RP6conrad/ESP-GPS-Logger/Ublox.cpp

#include "Ublox.h"
#include "Definitions.h"
//#include <EEPROM.h>
int Time_Set_OK;
bool Nav_rate_NACK = false;
bool High_nav_rate_ACK = false;
bool check_M10_nav_rate = false;

UBXMessage ubxMessage = {000000000000};//definition here, declaration in ublox.h !!
struct tm tmstruct ;
struct tm my_time;  // time elements structure
time_t unix_timestamp; // a timestamp

void Ublox_on(){
  pinMode(UBLOX_POWER1, OUTPUT);//Power beitian //default drive strength 2, only 2.7V @ ublox gps
  pinMode(UBLOX_POWER2, OUTPUT);//Power beitian
  pinMode(UBLOX_POWER3, OUTPUT);//Power beitiansee
  rtc_gpio_set_drive_capability(UBLOX_RTC_GPIO1,GPIO_DRIVE_CAP_3);// https://www.esp32.com/viewtopic.php?t=5840
  rtc_gpio_set_drive_capability(UBLOX_RTC_GPIO2,GPIO_DRIVE_CAP_3);//3.0V @ ublox gps current 50 mA
  gpio_set_drive_capability(UBLOX_GPIO3,GPIO_DRIVE_CAP_3);//rtc_gpio_ necessary, if not no output on RTC_pins 25 en 26, 13/3/2022
  delay(50);
  digitalWrite(UBLOX_POWER1, HIGH); 
  digitalWrite(UBLOX_POWER2, HIGH);
  digitalWrite(UBLOX_POWER3, HIGH);
  delay(100);
}
void Ublox_off(){
  digitalWrite(UBLOX_POWER1, LOW);
  digitalWrite(UBLOX_POWER2, LOW);
  digitalWrite(UBLOX_POWER3, LOW);
 // rtc_gpio_deinit(UBLOX_RTC_GPIO1);
 // rtc_gpio_deinit(UBLOX_RTC_GPIO2);
}
void Ublox_serial2(int delay_ms){
 for(int i=0;i<delay_ms;i++){
     int msgType = processGPS();
     if ( msgType == MT_NAV_ACK){
          Serial.print(" ACK ");
          Serial.print (ubxMessage.navAck.msg_cls);
          Serial.println (ubxMessage.navAck.msg_id);
          if(check_M10_nav_rate) High_nav_rate_ACK = true;
          }
     if ( msgType == MT_NAV_NACK){
          Serial.print(" NACK ");
          Serial.print (ubxMessage.navNack.msg_cls);
          Serial.println (ubxMessage.navNack.msg_id);
          if(check_M10_nav_rate) Nav_rate_NACK = true;
          }          
     if ( msgType == MT_NAV_ID){
          Serial.print("ID= :");
          Serial.print (ubxMessage.ubxId.ubx_id_1);
          Serial.print (ubxMessage.ubxId.ubx_id_2);
          Serial.print (ubxMessage.ubxId.ubx_id_3);
          Serial.print (ubxMessage.ubxId.ubx_id_4);
          Serial.println(ubxMessage.ubxId.ubx_id_5);
          }
     if ( msgType == MT_MON_GNSS){
          Serial.print("GNSS= :");
          Serial.print (ubxMessage.monGNSS.supported_Gnss);
          Serial.print (ubxMessage.monGNSS.default_Gnss);
          Serial.println (ubxMessage.monGNSS.enabled_Gnss);
          }
      if ( msgType == MT_MON_VER){
          Serial.print("SW Ublox=");
          Serial.println(ubxMessage.monVER.swVersion);
          Serial.print ("HW Ublox=");
          Serial.println (ubxMessage.monVER.hwVersion);
          }    
     delay(2);   
     } 
}
//Initialization of the ublox M8N with binary commands
void Init_ublox(void){
  int wait=250;
  char M8_9600_bd[20]="Ublox M8 9600bd";
  char M8_38400_bd[20]="Ublox M8 38400bd";
  if(config.ublox_type==M8_9600BD) strcpy(Ublox_type,M8_9600_bd);
  if(config.ublox_type==M8_38400BD) strcpy(Ublox_type,M8_38400_bd);
  /*send configuration data in UBX protocol is already done in SetupGPS()
  Serial.println("Set ublox UBX_OUT ");     
  for(int i = 0; i < sizeof(UBLOX_UBX_BD9600); i++) {                        
        Serial2.write( pgm_read_byte(UBLOX_UBX_BD9600+i) );
        }
  Ublox_serial2(wait); 
  */
  if(config.dynamic_model==1){
      Serial.println("Set ublox UBX_SEA ");
      for(int i = 0; i < sizeof(UBX_SEA); i++) {                        
        Serial2.write( pgm_read_byte(UBX_SEA+i) );
        }
  Ublox_serial2(wait);       
  }
  if(config.dynamic_model==2){
      Serial.println("Set ublox UBX_AUTOMOTIVE ");
      for(int i = 0; i < sizeof(UBX_AUTOMOTIVE); i++) {                        
        Serial2.write( pgm_read_byte(UBX_AUTOMOTIVE+i) );
        }
  Ublox_serial2(wait); 
  }
  //gnss 4 = GPS + GALILEO + BEIDOU  (default M10)
  //gnss x = GPS + GLONASS + BEIDOU   (impossible for the M10 ???)
  //gnss 3 = GPS + GLONASS + GALILEO
  //gnss 2 = GPS + GLONASS (default M8 ROM 2)
  //gnss 1 = GPS + GALILEO (not working for M8)
  //gnss 0 = GPS + BEIDOU  
    if(config.gnss==1){
      Serial.println("Set ublox UBX_GNSS2 : GPS + BEIDOU ");
      for(int i = 0; i < sizeof(UBX_GNSS2_GPS_BEIDOU); i++) {                        
        Serial2.write( pgm_read_byte(UBX_GNSS2_GPS_BEIDOU+i) );
        }
      Ublox_serial2(wait); 
      }
  if(config.gnss==3){
      Serial.println("Set ublox UBX_GNSS3 : GPS, GLONASS & GALILEO ");
      for(int i = 0; i < sizeof(UBX_GNSS3); i++) {                        
        Serial2.write( pgm_read_byte(UBX_GNSS3+i) );
        }
      Ublox_serial2(wait); 
      }
  if(config.gnss==4){
      Serial.println("Set ublox UBX_GNSS3 : GPS, GLONASS & BEIDOU ");
      for(int i = 0; i < sizeof(UBX_GNSS3_BEIDOU); i++) {                        
        Serial2.write( pgm_read_byte(UBX_GNSS3_BEIDOU+i) );
        }
      Ublox_serial2(wait); 
      }
  Serial.println("Check MON_GNSS settings ");
  for(int i = 0; i < sizeof(UBX_MON_GNSS); i++) {                        
      Serial2.write( pgm_read_byte(UBX_MON_GNSS+i) );
      }
  Ublox_serial2(wait); 
  Serial.print("Ask ublox Unique ID ");     
  for(int i = 0; i < sizeof(UBX_ID); i++) {                        
        Serial2.write( pgm_read_byte(UBX_ID+i) );
        }
  Ublox_serial2(wait);
  Serial.println("Check UBX_MON_VER ");     
   for(int i = 0; i < sizeof(UBX_MON_VER); i++) {                        
        Serial2.write( pgm_read_byte(UBX_MON_VER+i) );        
        }                 
  Ublox_serial2(wait);
  Serial.println("Set ublox NAV_PVT_ON ");   
  for(int i = 0; i < sizeof(UBLOX_UBX_NAVPVT_ON); i++) {                        
        Serial2.write( pgm_read_byte(UBLOX_UBX_NAVPVT_ON+i) );
        }
  Ublox_serial2(wait);         
  Serial.println("Set ublox NAV_DOP_ON ");   
  for(int i = 0; i < sizeof(UBLOX_UBX_NAVDOP_ON); i++) {                        
        Serial2.write( pgm_read_byte(UBLOX_UBX_NAVDOP_ON+i) );
        }
  Ublox_serial2(wait); 
  if((config.logUBX_nav_sat)&(config.logUBX)){
      Serial.println("Set ublox NAV_SAT_ON ");   
      for(int i = 0; i < sizeof(UBLOX_UBX_NAVSAT_ON); i++) {                        
            Serial2.write( pgm_read_byte(UBLOX_UBX_NAVSAT_ON+i) );
            }
      Ublox_serial2(wait);   
      }
  Serial.println("Set ublox to 38400BD "); 
  for(int i = 0; i < sizeof(UBLOX_UBX_BD38400); i++) {                        
        Serial2.write( pgm_read_byte(UBLOX_UBX_BD38400+i) );
        //delay(5); // simulating a 38400baud pace (or less), otherwise commands are not accepted by the device.
        } 
  Serial2.flush();
  Serial2.begin(38400,SERIAL_8N1, RXD2, TXD2);//in Init_ublox last command is change baudrate to 19200, necessary for 10 Hz  NAV_PVT + NAV_DOP!!!
  Ublox_serial2(wait);    
}
//Initialization of the ublox M8N  rate with binary commands, choice between 1..4
void Set_rate_ublox(int rate){
  int sample_rate=2;
  switch(rate){
    case 1:sample_rate=2;break;
    case 2:sample_rate=3;break;
    case 4:sample_rate=4;break;
    case 5:sample_rate=5;break;
    case 8:sample_rate=6;break;
    case 10:sample_rate=7;break;
    case 18:sample_rate=8;break;
    default:sample_rate=2;
    config.sample_rate=1;
    }
  Serial.print("Set rate Ublox ");
  for(int i = (sample_rate*14-14); i < sample_rate*14; i++) {                        
        Serial2.write( pgm_read_byte(UBLOX_RATE+i) );
        }
  Ublox_serial2(500);      
}
void sendNavSpgInfilMaxSvs(uint8_t maxSvs) {
  if(maxSvs<10)maxSvs=10;
  uint8_t packet[17] = {
    0xB5, 0x62,             // Sync
    0x06, 0x8A,             // Class, ID
    0x09, 0x00,             // Payload Length (9)
    0x00,                   // Version
    0x01,                   // Layer: 0x01 = RAM
    0x00, 0x00,             // Reserved
    0xA2, 0x00, 0x11, 0x20, // Key ID (Little Endian)
    maxSvs,                 // De dynamische waarde
    0x00, 0x00              // Placeholder for CK_A, CK_B
  };
  uint8_t ck_a = 0;
  uint8_t ck_b = 0;
  // Calculate checksum start at index 2 (Class/ID to Value)
  for (int i = 2; i < 15; i++) {
    ck_a += packet[i];
    ck_b += ck_a;
  }
  // add checksum last 2 bytes
  packet[15] = ck_a;
  packet[16] = ck_b;
  // send to gps module
  Serial2.write(packet, sizeof(packet));
  Ublox_serial2(500);   //wait for response
}

//Initialization of the ublox M10N with binary commands
void Init_ubloxM10(void){
  int wait=250;
  char M9_9600_bd[20]="Ublox M9 9600bd";
  char M9_38400_bd[20]="Ublox M9 38400bd";
  char M9_115200_bd[20]="Ublox M9 115200bd";
  char M10_9600_bd[20]="Ublox M10 9600bd";
  char M10_38400_bd[20]="Ublox M10 38400bd";
  char M10_115200_bd[20]="Ublox M10 115200bd";
  if(config.ublox_type==M9_9600BD) strcpy(Ublox_type,M9_9600_bd);
  if(config.ublox_type==M9_38400BD) strcpy(Ublox_type,M9_38400_bd);
  if(config.ublox_type==M9_115200BD) strcpy(Ublox_type,M9_115200_bd);
  if(config.ublox_type==M10_9600BD) strcpy(Ublox_type,M10_9600_bd);
  if(config.ublox_type==M10_38400BD) strcpy(Ublox_type,M10_38400_bd);
  if(config.ublox_type==M10_115200BD) strcpy(Ublox_type,M10_115200_bd);
  //send configuration data in UBX protocol 
  Serial.println("Set ublox M10 NMEA OFF ");     
  for(int i = 0; i < sizeof(UBLOX_M10_NMEA_OFF); i++) {                        
        Serial2.write( pgm_read_byte(UBLOX_M10_NMEA_OFF+i) );
        }
  Ublox_serial2(wait); 
  if((config.ublox_type == M10_9600BD)|(config.ublox_type == M10_38400BD)|(config.ublox_type == M10_115200BD)){
    if(config.M10_high_nav == SET_M10_HIGH_NAV){ Set_M10_high_nav_rate();}//reboot noodzakelijk ????
    //config.M10_high_nav=Check_M10_nav_rate();
    }
   
  if(config.dynamic_model==1){
      Serial.println("Set ublox UBX_M10_SEA ");
      for(int i = 0; i < sizeof(UBX_M10_SEA); i++) {                        
        Serial2.write( pgm_read_byte(UBX_M10_SEA+i) );
        }
  Ublox_serial2(wait);       
  }
  if(config.dynamic_model==2){
      Serial.println("Set ublox UBX_M10_AUTOMOTIVE ");
      for(int i = 0; i < sizeof(UBX_M10_AUTOMOTIVE); i++) {                        
        Serial2.write( pgm_read_byte(UBX_M10_AUTOMOTIVE+i) );
        }
  Ublox_serial2(wait); 
  }
  //Default M10 = GPS+GALILEO+BEIDOU
  //GNSS 5 = GPS + GALILEO + GLONASS + BEIDOU (only M9)
  //gnss 4 = GPS + GALILEO + BEIDOU_B1C  (default is beidou B1L !! M10)
  //gnss x = GPS + GLONASS + BEIDOU (switch off QZSS first M10 !!!)
  //gnss 3 = GPS + GLONASS + GALILEO
  //gnss 2 = GPS + GLONASS
  //gnss 1 = GPS + GALILEO
  
  if(config.gnss==4){   //for M9, default is 4 GNSS activated, config.gnss=6  !!
        Serial.println("Set ublox M10 GLONASS OFF ");     
        for(int i = 0; i < sizeof(UBLOX_M10_GLONASS_OFF); i++) {                        
              Serial2.write( pgm_read_byte(UBLOX_M10_GLONASS_OFF+i) );
              }
        Ublox_serial2(wait);
        Serial.println("Set ublox M10 BEIDOU B1 OFF ");     
        for(int i = 0; i < sizeof(UBLOX_M10_BEIDOU_B1_OFF); i++) {                        
              Serial2.write( pgm_read_byte(UBLOX_M10_BEIDOU_B1_OFF+i) );
              }
        Ublox_serial2(wait);
        Serial.println("Set ublox M10 BEIDOU B1C ON ");     
        for(int i = 0; i < sizeof(UBLOX_M10_BEIDOU_B1C_ON); i++) {                        
              Serial2.write( pgm_read_byte(UBLOX_M10_BEIDOU_B1C_ON+i) );
              }
        Ublox_serial2(wait);
        }     
  if(((config.gnss==5)&(config.sample_rate<10)&((config.ublox_type == M10_9600BD)|(config.ublox_type == M10_38400BD)|(config.ublox_type == M10_115200BD)))){  
        Serial.println("Set ublox M10 4 GNSS ");     
        for(int i = 0; i < sizeof(UBLOX_M10_4GNSS); i++) {                        
              Serial2.write( pgm_read_byte(UBLOX_M10_4GNSS+i) );
              }
        Ublox_serial2(wait);
        }            
  if(config.gnss==3){          
      Serial.println("Set ublox M10 BEIDOU OFF ");     
      for(int i = 0; i < sizeof(UBLOX_M10_BEIDOU_OFF); i++) {                        
            Serial2.write( pgm_read_byte(UBLOX_M10_BEIDOU_OFF+i) );
            }
      Ublox_serial2(wait);  
      Serial.println("Set ublox M10 GLONASS ON ");     
      for(int i = 0; i < sizeof(UBLOX_M10_GLONASS_ON); i++) {                        
            Serial2.write( pgm_read_byte(UBLOX_M10_GLONASS_ON+i) );
            }
      Ublox_serial2(wait);      
      } 
  if(config.gnss==2){          
      Serial.println("Set ublox M10 GALILEO OFF ");     
      for(int i = 0; i < sizeof(UBLOX_M10_GAL_OFF); i++) {                        
            Serial2.write( pgm_read_byte(UBLOX_M10_GAL_OFF+i) );
            }
      Ublox_serial2(wait);
      Serial.println("Set ublox M10 BEIDOU OFF ");     
      for(int i = 0; i < sizeof(UBLOX_M10_BEIDOU_OFF); i++) {                        
            Serial2.write( pgm_read_byte(UBLOX_M10_BEIDOU_OFF+i) );
            }
      Ublox_serial2(wait);  
      Serial.println("Set ublox M10 GLONASS ON ");     
      for(int i = 0; i < sizeof(UBLOX_M10_GLONASS_ON); i++) {                        
            Serial2.write( pgm_read_byte(UBLOX_M10_GLONASS_ON+i) );
            }
      Ublox_serial2(wait);      
      }
  if(config.gnss==1){     
      Serial.println("Set ublox M10 BEIDOU OFF ");     
      for(int i = 0; i < sizeof(UBLOX_M10_BEIDOU_OFF); i++) {                        
            Serial2.write( pgm_read_byte(UBLOX_M10_BEIDOU_OFF+i) );
            }
      Ublox_serial2(wait);      
      Serial.println("Set ublox M10 GLONASS OFF ");     
      for(int i = 0; i < sizeof(UBLOX_M10_GLONASS_OFF); i++) {                        
            Serial2.write( pgm_read_byte(UBLOX_M10_GLONASS_OFF+i) );
            }
      Ublox_serial2(wait);      
      }         
  Serial.println("Set ublox M10 UBX On ");     
  for(int i = 0; i < sizeof(UBLOX_M10_UBX); i++) {                        
        Serial2.write( pgm_read_byte(UBLOX_M10_UBX+i) );
        }
  Ublox_serial2(wait);    
  Serial.println("Set ublox M10 NAV_PVT_ON ");   
  for(int i = 0; i < sizeof(UBLOX_M10_NAV_PVT); i++) {                        
        Serial2.write( pgm_read_byte(UBLOX_M10_NAV_PVT+i) );
        }
  Ublox_serial2(wait);         
  Serial.println("Set ublox M10 NAV_DOP_ON ");   
  for(int i = 0; i < sizeof(UBLOX_M10_NAV_DOP); i++) {                        
        Serial2.write( pgm_read_byte(UBLOX_M10_NAV_DOP+i) );
        }
  /**     
  if(config.M10_full_power){
    Serial.println("Set ublox M10 full power ON ");   
    for(int i = 0; i < sizeof(UBX_M10_FULL_POWER_MODE); i++) {                        
          Serial2.write( pgm_read_byte(UBX_M10_FULL_POWER_MODE+i) );
          }      
    Ublox_serial2(wait);
    } 
  */  
  Serial.println("Set ublox max_Svs ");   
  sendNavSpgInfilMaxSvs(config.max_Svs); //max satellites in nav solution  
  Serial.println("Set ublox min elevation Sats ");  
  build_ubx_cfg_min_elevation(config.M10_min_elevation); //minimal elevation above horizon

  if((config.logUBX_nav_sat)&(config.logUBX)){
      Serial.println("Set ublox M10 NAV_SAT_ON "); 
      if(config.sample_rate<10){ 
        for(int i = 0; i < sizeof(UBLOX_M10_NAV_SAT); i++) {     //NAV_SAT_RATE = sample_rate/10                   
        Serial2.write( pgm_read_byte(UBLOX_M10_NAV_SAT+i) );
        }
      } 
      else{
        for(int i = 0; i < sizeof(UBLOX_M9_NAV_SAT); i++) {       //NAV_SAT_RATE = sample_rate/40                  
        Serial2.write( pgm_read_byte(UBLOX_M9_NAV_SAT+i) );
        }  
      }
      Ublox_serial2(wait);
    }       
  Serial.println("Check UBX_MON_VER ");  //does this work for the M10 ??   
   for(int i = 0; i < sizeof(UBX_MON_VER); i++) {                        
        Serial2.write( pgm_read_byte(UBX_MON_VER+i) );        
        }           
  Ublox_serial2(wait); 
  Serial.println("Check MON_GNSS settings ");
  for(int i = 0; i < sizeof(UBX_MON_GNSS); i++) {                        
      Serial2.write( pgm_read_byte(UBX_MON_GNSS+i) );
      }
  Ublox_serial2(wait);      
  Serial.print("Ask ublox Unique ID ");     
  for(int i = 0; i < sizeof(UBX_ID); i++) {                        
        Serial2.write( pgm_read_byte(UBX_ID+i) );
        }  
  Ublox_serial2(wait); 
  Serial.println("Set ublox M10 to 38400BD "); 
  for(int i = 0; i < sizeof(UBLOX_M10_UBX_BD38400); i++) {                        
        Serial2.write( pgm_read_byte(UBLOX_M10_UBX_BD38400+i) );
        //delay(5); // simulating a 38400baud pace (or less), otherwise commands are not accepted by the device.
        } 
  Serial2.flush();
  Serial2.begin(38400,SERIAL_8N1, RXD2, TXD2);//in Init_ublox last command is change baudrate to 38400, necessary for 10 Hz  NAV_PVT + NAV_DOP!!!
  Ublox_serial2(wait);   
}
//Initialization of the ublox M10N  rate with binary commands, choice between 1..5
void Set_rate_ubloxM10(int rate){
  int sample_rate=2;
  switch(rate){
    case 1:sample_rate=1;break;
    case 2:sample_rate=2;break;
    case 4:sample_rate=3;break;
    case 5:sample_rate=4;break;
    case 8:sample_rate=5;break;
    case 10:sample_rate=6;break;
    case 15:sample_rate=7;break;
    case 20:sample_rate=8;break;
    default:sample_rate=1;
    config.sample_rate=1;
    }
  Serial.print("Set rate Ublox M10");
  for(int i = (sample_rate*18-18); i < sample_rate*18; i++) {                        
        Serial2.write( pgm_read_byte(UBLOX_M10_RATE+i) );
        }
  Ublox_serial2(500);      
}
int Set_GPS_Time(float time_offset){    
  // convert a date and time into unix time
        if(ubxMessage.navPvt.year<2023) {
          //Serial.println("GPS Reported year not plausible (<2023) !");
          return false; 
          }//check if year is plausible 
        my_time.tm_sec = ubxMessage.navPvt.second;
        my_time.tm_hour = ubxMessage.navPvt.hour;
        my_time.tm_min = ubxMessage.navPvt.minute;
        my_time.tm_mday = ubxMessage.navPvt.day;
        my_time.tm_mon = ubxMessage.navPvt.month-1;  //mktime needs months 0 - 11  
        my_time.tm_year = ubxMessage.navPvt.year - 1900; // mktime needs years since 1900, so deduct 1900
        //my_time.tm_isdst = 1;//daylight timesaving active
        //# define DLS
        #if defined(DLS)
        //summertime is on march 26 2023 2 AM, see https://www.di-mgt.com.au/wclock/help/wclo_tzexplain.html     
        my_time.tm_hour = 2;
        my_time.tm_min = 58;
        my_time.tm_mday =26;
        my_time.tm_mon = 2;  //mktime needs months 0 - 11  
        my_time.tm_year = 2023 - 1900; 
        #endif
        setenv("TZ","GMT0",1);//neede if time is set again (gps sets time double)
        tzset();
        unix_timestamp =  mktime(&my_time);//mktime returns local time, so TZ is important !!!
        struct timeval tv = { .tv_sec = (time_t)(unix_timestamp), .tv_usec = 0 };  //clean utc time !!     
        settimeofday(&tv, NULL);
        setenv("TZ",TimeZone,1);
        tzset();     //this works for CET, but TZ string is different for every Land / continent....
        delay(10);//
        if(!getLocalTime(&tmstruct)){
            Serial.println("Can't get time1...");
            return false;
            }
        if((tmstruct.tm_year+1900)<2023){
          Serial.printf("\nNow is : %d-%02d-%02d %02d:%02d:%02d\n",(tmstruct.tm_year)+1900,( tmstruct.tm_mon)+1, tmstruct.tm_mday,tmstruct.tm_hour , tmstruct.tm_min, tmstruct.tm_sec);
          //Serial.println("GPS Reported year not plausible (<2023) !");
          return false; 
          }
        Serial.println("GPS Local Time is set");
        return true;
}

// The last two bytes of the message is a checksum value, used to confirm that the received payload is valid.
// The procedure used to calculate this is given as pseudo-code in the uBlox manual.
void calcChecksum(unsigned char* CK,int msgType, int msgSize) {
  memset(CK, 0, 2);
  for (int i = 0; i < msgSize; i++) {
    if(msgType==MT_NAV_PVT) {CK[0] += ((unsigned char*)(&ubxMessage.navPvt))[i];}
    else if(msgType==MT_NAV_DOP) {CK[0] += ((unsigned char*)(&ubxMessage.navDOP))[i];} 
    else if(msgType==MT_MON_GNSS){CK[0] += ((unsigned char*)(&ubxMessage.monGNSS))[i];} 
    else if(msgType==MT_MON_VER){CK[0] += ((unsigned char*)(&ubxMessage.monVER))[i];} 
    else if(msgType==MT_NAV_ACK){CK[0] += ((unsigned char*)(&ubxMessage.navAck))[i];} 
    else if(msgType==MT_NAV_NACK){CK[0] += ((unsigned char*)(&ubxMessage.navNack))[i];} 
    else if(msgType==MT_NAV_SAT){CK[0] += ((unsigned char*)(&ubxMessage.navSat))[i];} 
    else if(msgType==MT_NAV_ID){CK[0] += ((unsigned char*)(&ubxMessage.ubxId))[i];} 
    else {CK[0] += ((unsigned char*)(&ubxMessage))[i];}
    CK[1] += CK[0];
  }
}
// Compares the first two bytes of the ubxMessage struct with a specific message header.
// Returns true if the two bytes match (0xB5 0x62).
boolean compareMsgHeader(const unsigned char* msgHeader) {
  unsigned char* ptr = (unsigned char*)(&ubxMessage.navDummy);
  return ptr[0] == msgHeader[0] && ptr[1] == msgHeader[1];
}
// Reads in bytes from the GPS module and checks to see if a valid message has been constructed.
// Returns the type of the message found if successful, or MT_NONE if no message was found.
// After a successful return the contents of the ubxMessage union will be valid, for the 
// message type that was found. As now every message has its own struct, further calls to this function can invalidate the
// message content if the message was the same, so you must use the obtained values before calling this function again.

int processGPS() {
  static int fpos = 0;
  static unsigned char checksum[2];
  static byte currentMsgType = MT_NONE;
  static int payloadSize = sizeof(ubxMessage.navDummy);
  //static uint16_t len;//10 Hz M10 issue ??
  while ( Serial2.available() ) {
    byte c = Serial2.read();    
    //Serial.write(c);
    if ( fpos < 2 ) {
      // For the first two bytes we are simply looking for a match with the UBX header bytes (0xB5,0x62)
      if ( c == UBX_HEADER[fpos] )
        fpos++;
      else
        fpos = 0; // Reset to beginning state.
    }
    else {
      // If we come here then fpos >= 2, which means we have found a match with the UBX_HEADER
      // and we are now reading in the bytes that make up the payload.
      // Place the incoming byte into the ubxMessage.navDummy struct. The position is fpos-2 because
      // the struct does not include the initial two-byte header (UBX_HEADER).
      // the struct does not include the 2 last bytes which are the checksums
      // checksums are not placed in the ubxMessage !!!
      if (((fpos-2) < payloadSize)&(fpos<4)){((unsigned char*)(&ubxMessage.navDummy))[fpos-2] = c;} 
      if(fpos==3) {
        // We have just received the second byte of the message type header, 
        // so now we can check to see what kind of message it is.
        //We have to restore cls and id to the correct substructure
        if ( compareMsgHeader(NAV_PVT_HEADER) ) {
          currentMsgType = MT_NAV_PVT;
          payloadSize = sizeof(NAV_PVT);
          ubxMessage.navPvt.cls=ubxMessage.navDummy.cls;
          ubxMessage.navPvt.id=ubxMessage.navDummy.id;
          //Serial.print("hPVT ");
        }
        else if ( compareMsgHeader(MON_GNSS_HEADER) ) {
          currentMsgType = MT_MON_GNSS;
          payloadSize = sizeof(MON_GNSS);
          ubxMessage.monGNSS.cls=ubxMessage.navDummy.cls;
          ubxMessage.monGNSS.id=ubxMessage.navDummy.id;
          //Serial.println("MT_MON_GNSS\n");
        }
        else if ( compareMsgHeader(NAV_DOP_HEADER) ) {
          currentMsgType = MT_NAV_DOP;
          payloadSize = sizeof(NAV_DOP);
          ubxMessage.navDOP.cls=ubxMessage.navDummy.cls;
          ubxMessage.navDOP.id=ubxMessage.navDummy.id;
          //Serial.print("hDOP ");
        }
        else if ( compareMsgHeader(MON_VER_HEADER) ) {
          currentMsgType = MT_MON_VER;
          payloadSize = sizeof(MON_VER);
          ubxMessage.monVER.cls=ubxMessage.navDummy.cls;
          ubxMessage.monVER.id=ubxMessage.navDummy.id;
          //Serial.println("MT_MON_VER\n");
        }
        else if ( compareMsgHeader(NAV_ACK_HEADER) ) {
          currentMsgType = MT_NAV_ACK;
          payloadSize = sizeof(NAV_ACK);
          ubxMessage.navAck.cls=ubxMessage.navDummy.cls;
          ubxMessage.navAck.id=ubxMessage.navDummy.id;
          //Serial.println("NAV_ACK\n");
        }
        else if ( compareMsgHeader(NAV_NACK_HEADER) ) {
          currentMsgType = MT_NAV_NACK;
          payloadSize = sizeof(NAV_NACK);
          ubxMessage.navNack.cls=ubxMessage.navDummy.cls;
          ubxMessage.navNack.id=ubxMessage.navDummy.id;
          //Serial.println("NAV_NACK\n");
        }
        else if ( compareMsgHeader(NAV_SAT_HEADER) ) {
          currentMsgType = MT_NAV_SAT;
          ubxMessage.navSat.cls=ubxMessage.navDummy.cls;
          ubxMessage.navSat.id=ubxMessage.navDummy.id;
          //Serial.println("NAV_SAT\n");
        }
        else if ( compareMsgHeader(NAV_ID_HEADER) ) {
          currentMsgType = MT_NAV_ID;
          ubxMessage.ubxId.cls=ubxMessage.navDummy.cls;
          ubxMessage.ubxId.id=ubxMessage.navDummy.id;
          //Serial.println("NAV_ID\n");
        }
        else {
          // unknown message type, bail
          currentMsgType = MT_NONE;
          fpos = 0;
          continue;
        }
      }
      if (((fpos-2) < payloadSize)&(fpos>=4)){
        if(currentMsgType==MT_NAV_PVT) {((unsigned char*)(&ubxMessage.navPvt))[fpos-2] = c;} 
        if(currentMsgType==MT_NAV_DOP) {((unsigned char*)(&ubxMessage.navDOP))[fpos-2] = c;} 
        if(currentMsgType==MT_MON_GNSS) {((unsigned char*)(&ubxMessage.monGNSS))[fpos-2] = c;} 
        if(currentMsgType==MT_MON_VER) {((unsigned char*)(&ubxMessage.monVER))[fpos-2] = c;} 
        if(currentMsgType==MT_NAV_ACK) {((unsigned char*)(&ubxMessage.navAck))[fpos-2] = c;} 
        if(currentMsgType==MT_NAV_NACK) {((unsigned char*)(&ubxMessage.navNack))[fpos-2] = c;} 
        if(currentMsgType==MT_NAV_SAT) {((unsigned char*)(&ubxMessage.navSat))[fpos-2] = c;}
        if(currentMsgType==MT_NAV_ID) {((unsigned char*)(&ubxMessage.ubxId))[fpos-2] = c;}  
      }
       if (fpos==6){
        if(currentMsgType==MT_NAV_PVT){ubxMessage.navPvt.len=payloadSize-6;}//safety if .len is wrong
        if(currentMsgType==MT_NAV_DOP){ubxMessage.navDOP.len=payloadSize-6;}//safety if .len is wrong
        if(currentMsgType==MT_NAV_ID){ payloadSize=ubxMessage.ubxId.len+6;}// .len = 9 bytes for M8, but 10 bytes for M10
        if(currentMsgType==MT_MON_VER){
            if(ubxMessage.monVER.len+6<sizeof(ubxMessage.monVER)){
                payloadSize=ubxMessage.monVER.len+6;
                }//M10 has extensions ??
            else{fpos=0;}//something went wrong, start over again !!!
            }          
        if(currentMsgType==MT_NAV_SAT){
            if(ubxMessage.navSat.len+6<sizeof(ubxMessage.navSat)){//safety if .len is wrong
                payloadSize=ubxMessage.navSat.len+6;
                }//payload is variable with nav_sat msg
            else{fpos=0;}//something went wrong, start over again !!!
            }
      }
      fpos++;
      if ( fpos == (payloadSize) ) {//was (payloadSize+2)
      // All payload bytes have now been received, so we can calculate the 
      // expected checksum value to compare with the next two incoming bytes.
      // checksum has to calculated out of the correct substructure !!!
        calcChecksum(checksum,currentMsgType,payloadSize-2);//was payload !!
      }
      else if ( fpos == (payloadSize+1) ) {//was (payloadSize+3)   fpos-3=c, of payloadsize+1-3=c, dus payloadsize-2
        // First byte after the payload, ie. first byte of the checksum.
        // Does it match the first byte of the checksum we calculated?

        if ( c != checksum[0] ) {
          // Checksum doesn't match, reset to beginning state and try again.
           Serial.println("CkA NIO");
         if ((Time_Set_OK==true)&(nav_pvt_message>10)){
              char tekst[32] = "";
              sprintf(tekst, "ChecksumA_NIO @ %d\n", (nav_pvt_message-11));
              logERR(tekst);
            }
          fpos = 0; 
        }
      }
      else if ( fpos == (payloadSize+2) ) {//was (payloadSize+4)  fpos-4=c, of payloadsize+1-4=c, dus payloadsize-1
        // Second byte after the payload, ie. second byte of the checksum.
        // Does it match the second byte of the checksum we calculated?
        fpos = 0; // We will reset the state regardless of whether the checksum matches.
        if ( c == checksum[1] ) {
          // Checksum matches, we have a valid message.
          /* iTow has a 18 s diff with UTC, issue with GPS Results !!
           if(currentMsgType==MT_NAV_SAT){
              ubxMessage.navSat.iTOW=ubxMessage.navSat.iTOW-18*1000;//to match 18s diff UTC nav pvt & GPS nav sat !!!
              calcChecksum(checksum,currentMsgType,payloadSize-2);//have to calculate new checksum !!
              ((unsigned char*)(&ubxMessage.navSat))[payloadSize-2]=checksum[0];//checksum is not on a fixed pos, depends from the payload !!!
              ((unsigned char*)(&ubxMessage.navSat))[payloadSize-1]=checksum[1];//checksum is not on a fixed pos, depends from the payload !!!
            }
          */ 
          return currentMsgType; 
        }
        else{ if ((Time_Set_OK==true)&(nav_pvt_message>10)){
              Serial.println("CkB NIO");
              char tekst[32] = "";
              sprintf(tekst, "ChecksumB_NIO @ %d\n", (nav_pvt_message-11));
              logERR(tekst);
              }
            }
      }    
      else if ( fpos > (payloadSize+2) ) {//was (payloadSize+4)
        // We have now read more bytes than both the expected payload and checksum 
        // together, so something went wrong. Reset to beginning state and try again.
        fpos = 0;
      }
    }
  }
  return MT_NONE;
}
int Auto_detect_ublox(){
  config.ublox_type=0;
  bool Ublox_M10=false;
  Serial.println("Check UBX_MON_VER @9600bd ");  //check for 9600 bd ??   
  for(int i = 0; i < sizeof(UBX_MON_VER); i++) {                        
        Serial2.write( pgm_read_byte(UBX_MON_VER+i) );        
        }           
  Ublox_serial2(1000); 
  Serial.println(ubxMessage.monVER.hwVersion[3]);
  if(ubxMessage.monVER.hwVersion[3]=='8'){
    config.ublox_type=M8_9600BD;
    Serial.println("Ublox M8 @9600bd ");
    }//M8@9600 bd
  if(ubxMessage.monVER.hwVersion[3]=='9'){
    config.ublox_type=M9_9600BD;
    Serial.println("Ublox M9 @9600bd ");
    }//M9@9600 bd  
  if(ubxMessage.monVER.hwVersion[3]=='A'){
    config.ublox_type=M10_9600BD;
    Serial.println("Ublox M10 @9600bd ");
    Ublox_M10=true;
    }//M10@9600 bd
  if(config.ublox_type==0){//no ublox @9600 bd detected
      //Serial2.flush();
      Serial2.begin(38400,SERIAL_8N1, RXD2, TXD2);// Change baudrate to 38400 for new test
      Serial2.flush();
      Serial.println("Check UBX_MON_VER @38400bd ");  //check for 9600 bd ?? 
      delay(100);  
      for(int i = 0; i < sizeof(UBX_MON_VER); i++) {                        
            Serial2.write( pgm_read_byte(UBX_MON_VER+i) );        
            }           
      Ublox_serial2(1000); 
      if(ubxMessage.monVER.hwVersion[3]=='8'){
        config.ublox_type=M8_38400BD;
        Serial.println("Ublox M8 @38400bd ");
        }//M8@384000 bd
      if(ubxMessage.monVER.hwVersion[3]=='9'){
        config.ublox_type=M9_38400BD;
        Serial.println("Ublox M9 @38400bd ");
        }//M8@384000 bd  
      if(ubxMessage.monVER.hwVersion[3]=='A'){
        config.ublox_type=M10_38400BD;
        Serial.println("Ublox M10 @38400bd ");
        Ublox_M10=true;
        }
      }
  if(config.ublox_type==0){//no ublox @9600 bd detected
      Serial2.begin(115200,SERIAL_8N1, RXD2, TXD2);// Change baudrate to 38400 for new test
      Serial2.flush();
      Serial.println("Check UBX_MON_VER @115200bd ");  //check for 9600 bd ?? 
      delay(100);  
      for(int i = 0; i < sizeof(UBX_MON_VER); i++) {                        
            Serial2.write( pgm_read_byte(UBX_MON_VER+i) );        
            }           
      Ublox_serial2(1000); 
      if(ubxMessage.monVER.hwVersion[3]=='8'){
        config.ublox_type=M8_115200BD;
        Serial.println("Ublox M8 @115200bd ");
        }
      if(ubxMessage.monVER.hwVersion[3]=='9'){
        config.ublox_type=M9_115200BD;
        Serial.println("Ublox M9 @115200bd ");
        } 
      if(ubxMessage.monVER.hwVersion[3]=='A'){
        config.ublox_type=M10_115200BD;
        Serial.println("Ublox M10 @115200bd ");
        Ublox_M10=true;
        }
      }  
    Serial.println(ubxMessage.monVER.hwVersion[3]) ; 
    if(Ublox_M10==true){
      config.M10_high_nav=Check_M10_nav_rate();
      //EEPROM.write(1,config.M10_high_nav);EEPROM.commit();
      preferences.begin("gps_config", false);
      config.M10_high_nav=Check_M10_nav_rate();
      preferences.putUChar("M10_high_nav",config.M10_high_nav);
      preferences.end();
      }
    return config.ublox_type;  
}
/*
int Check_M10_nav_rate(void){
  int result=NO_M10_GPS;
  check_M10_nav_rate=true;
  Serial.println("Get M10 NAV Rate ");
    for(int i = 0; i < sizeof(UBX_M10_GET_NAV_RATE); i++) {                        
    Serial2.write( pgm_read_byte(UBX_M10_GET_NAV_RATE+i) );
    }
  Nav_rate_NACK = false;
  High_nav_rate_ACK = false;      
  Ublox_serial2(500);
  check_M10_nav_rate = false;
  if(Nav_rate_NACK){ 
    Serial.println("M10 Default Nav Rate");
    result=M10_DEFAULT_NAV;
    if(EEPROM.readByte(1)!=M10_DEFAULT_NAV)EEPROM.writeByte(1,M10_DEFAULT_NAV); EEPROM.commit();
  }
  if(High_nav_rate_ACK){
    Serial.println("M10 High Nav Rate set");
    result=M10_HIGH_NAV_RATE;
    if(EEPROM.readByte(1)!=M10_HIGH_NAV_RATE)EEPROM.writeByte(1,M10_HIGH_NAV_RATE); EEPROM.commit();
    } 
    return result;       
  }
*/  
int Check_M10_nav_rate(void){
  int result = NO_M10_GPS;
  check_M10_nav_rate = true;
  Serial.println(F("Get M10 NAV Rate "));
  
  for(int i = 0; i < sizeof(UBX_M10_GET_NAV_RATE); i++) {                        
    Serial2.write( pgm_read_byte(UBX_M10_GET_NAV_RATE+i) );
  }
  
  Nav_rate_NACK = false;
  High_nav_rate_ACK = false;      
  Ublox_serial2(500);
  check_M10_nav_rate = false;
  
  if(Nav_rate_NACK){ 
    Serial.println(F("M10 Default Nav Rate"));
    result = M10_DEFAULT_NAV;
    
    // --- PREFERENCES UPDATE BIJ DEFAULT NAV ---
    preferences.begin("gps_config", false); // Open namespace in read-write modus
    if (preferences.getUChar("M10_high_nav", NO_M10_GPS) != M10_DEFAULT_NAV) {
      preferences.putUChar("M10_high_nav", M10_DEFAULT_NAV);
    }
    preferences.end(); // Sluit en sla direct op
  }
  
  if(High_nav_rate_ACK){
    Serial.println(F("M10 High Nav Rate set"));
    result = M10_HIGH_NAV_RATE;
    
    // --- PREFERENCES UPDATE BIJ HIGH NAV ---
    preferences.begin("gps_config", false); // Open namespace in read-write modus
    if (preferences.getUChar("M10_high_nav", NO_M10_GPS) != M10_HIGH_NAV_RATE) {
      preferences.putUChar("M10_high_nav", M10_HIGH_NAV_RATE);
    }
    preferences.end(); // Sluit en sla direct op
  }   
  return result;       
}

/*
int Set_M10_high_nav_rate(void){
  Serial.println("Set ublox UBX_M10 High Nav Rate");
  for(int i = 0; i < sizeof(UBX_M10_SET_HIGH_NAV_RATE); i++) {                        
     Serial2.write( pgm_read_byte(UBX_M10_SET_HIGH_NAV_RATE+i) );
     }
  Ublox_serial2(500); 
  config.ublox_type= UBLOX_TYPE_UNKNOWN;
  config.M10_high_nav= M10_HIGH_NAV_RATE;
  EEPROM.writeByte(0,UBLOX_TYPE_UNKNOWN);
  EEPROM.writeByte(1,M10_HIGH_NAV_RATE); EEPROM.commit();//always set EEPROM to default nav rate.....
  return config.M10_high_nav;
}  
*/
int Set_M10_high_nav_rate(void){
  Serial.println(F("Set ublox UBX_M10 High Nav Rate"));
  
  for(int i = 0; i < sizeof(UBX_M10_SET_HIGH_NAV_RATE); i++) {                        
     Serial2.write( pgm_read_byte(UBX_M10_SET_HIGH_NAV_RATE+i) );
  }
  Ublox_serial2(500); 
  
  config.ublox_type = UBLOX_TYPE_UNKNOWN;
  config.M10_high_nav = M10_HIGH_NAV_RATE;
  
  // --- PREFERENCES UPDATE ---
  preferences.begin("gps_config", false); // Open namespace in read-write modus
  
  preferences.putUChar("ublox_type", UBLOX_TYPE_UNKNOWN);
  preferences.putUChar("M10_high_nav", M10_HIGH_NAV_RATE);
  
  preferences.end(); // Sluit de namespace en sla direct permanent op (vervangt commit)
  
  return config.M10_high_nav;
}



/**
 * Bouwt een UBX-CFG-VALSET pakket om de minimale satelliethoek (elevation mask) in te stellen.
 * 
 * @param buffer      Pointer naar een array van minimaal 17 bytes waar het pakket in wordt opgeslagen.
 * @param angle_deg   De gewenste hoek in graden (geldig bereik: 5 tot 25).
 * @param permanent   Als 1 (true): opslaan in RAM+BBR+Flash. Als 0 (false): alleen in RAM.
 */
void build_ubx_cfg_min_elevation(int8_t angle_deg) {
    // Validatie van de invoer (u-blox accepteert formeel -90 tot 90, maar we begrenzen op uw vraag)
    uint8_t buffer[17];
    if (angle_deg < 5 || angle_deg > 25 || buffer == NULL) {
        angle_deg=5; 
    }

    // 1. Sync Chars
    buffer[0] = 0xB5;
    buffer[1] = 0x62;

    // 2. Class & ID (UBX-CFG-VALSET = 0x06 0x8A)
    buffer[2] = 0x06;
    buffer[3] = 0x8A;

    // 3. Length (9 bytes payload -> Little Endian)
    buffer[4] = 0x09;
    buffer[5] = 0x00;

    // 4. Payload: Version (0)
    buffer[6] = 0x00;

    // 5. Payload: Layer (0x01 = RAM, 0x07 = RAM + BBR + Flash)
    buffer[7] = 0x01;

    // 6. Payload: Reserved (2 bytes)
    buffer[8] = 0x00;
    buffer[9] = 0x00;

    // 7. Payload: Configuration Key ID (0x201100a4 -> Little Endian)
    buffer[10] = 0xA4;
    buffer[11] = 0x00;
    buffer[12] = 0x11;
    buffer[13] = 0x20;

    // 8. Payload: Value (De gekozen hoek)
    buffer[14] = (uint8_t)angle_deg;

    // 9. Bereken Fletcher-8 Checksum over bytes 2 t/m 14
    uint8_t ck_a = 0;
    uint8_t ck_b = 0;
    
    for (size_t i = 2; i < 15; i++) {
        ck_a += buffer[i];
        ck_b += ck_a;
    }

    // 10. Voeg checksum toe aan het einde van de buffer
    buffer[15] = ck_a;
    buffer[16] = ck_b;
    for(int i = 0; i < sizeof(buffer); i++) {                        
      Serial2.write( buffer[i] );
      }
    Ublox_serial2(500);  //wait for response
}
