RP6conrad/ESP-GPS-Logger/SD_card.cpp

#include <LITTLEFS.h>
#include "Definitions.h"
#include "gpx.h"
#include "sbp.h"
#include "gpy.h"
File ubxfile;
File errorfile;
File gpyfile;  //new open source file format, work in progress !!
File sbpfile;
File gpxfile;
char filename_NO_EXT[64] = "/";
char filenameERR[64] = "/";
char filenameUBX[64] = "/";
char filenameGPY[64] = "/";
char filenameSBP[64] = "/";
char filenameGPX[64] = "/";
char dataStr[255] = "";  //string for logging  !!
char Buffer[50] = "";    //string for logging
uint64_t GPS_UTC_ms;     //Absolute UTC timewith ms resolution @start logging
int SD_MMC_read_speed;
int SD_MMC_write_speed;

struct Config config;

void logERR(const char *message) {
  if (config.logTXT) {
    errorfile.print(message);
  }
}
//test for existing GPSLOGxxxfiles, open txt,gps + ubx file with new name, or with timestamp !
void Open_files(void) {
  char macAddr[16];
  if (config.file_date_time) {
    getLocalTime(&tmstruct);
    char extension[16] = ".txt";  //
    char timestamp[16];

    if (config.file_date_time == 1) {
      sprintf(timestamp, "_%u%02u%02u%02u%02u", tmstruct.tm_year - 100, tmstruct.tm_mon + 1, tmstruct.tm_mday, tmstruct.tm_hour, tmstruct.tm_min);
      strcat(filenameERR, config.UBXfile);  //copy filename from config
      strcat(filenameERR, timestamp);       //add timestamp
      strcat(filenameERR, extension);       //add extension.txt
    }
    if (config.file_date_time == 2) {
      sprintf(timestamp, "%u%02u%02u%02u%02u_", tmstruct.tm_year - 100, tmstruct.tm_mon + 1, tmstruct.tm_mday, tmstruct.tm_hour, tmstruct.tm_min);
      strcat(filenameERR, timestamp);       //add timestamp
      strcat(filenameERR, config.UBXfile);  //copy filename from config
      strcat(filenameERR, extension);       //add extension.txt
    }
    if (config.file_date_time == 3) {
      sprintf(timestamp, "_%u%02u%02u%02u%02u", tmstruct.tm_year - 100, tmstruct.tm_mon + 1, tmstruct.tm_mday, tmstruct.tm_hour, tmstruct.tm_min);
      sprintf(macAddr, "_%2X%2X%2X", mac[3], mac[4], mac[5]);  //3 last bytes from MAC
      strcat(filenameERR, config.UBXfile);                    //copy filename from config
      strcat(filenameERR, timestamp);                         //add timestamp
      strcat(filenameERR, macAddr);
      strcat(filenameERR, extension);  //add extension.txt
    }
  } else {
    char txt[16] = "000.txt";
    sprintf(macAddr, "_%2X%2X%2X%2X%2X%2X_", mac[0], mac[1], mac[2], mac[3], mac[4], mac[5]);
    strcat(filenameERR, config.UBXfile);  //copy filename from config
    strcat(filenameERR, macAddr);
    int filenameSize = strlen(filenameERR);  //dit is dan 7 + NULL = 8
    strcat(filenameERR, txt);                //dit wordt dan /BN280A000.txt
    for (int i = 0; i < 1000; i++) {
      filenameERR[filenameSize + 2] = '0' + i % 10;
      filenameERR[filenameSize + 1] = '0' + ((i / 10) % 10);
      filenameERR[filenameSize] = '0' + ((i / 100) % 10);
      // create if does not exist, do not open existing, write, sync after write

      if (sdOK) {
        if (!SD_MMC.exists(filenameERR)) {
          break;
        }
      }
      if (LITTLEFS_OK) {
        if (!LITTLEFS.exists(filenameERR)) {
          break;
        }
      }
    }
  }
  strcpy(filename_NO_EXT, filenameERR);
  filename_NO_EXT[strlen(filename_NO_EXT) - 4 ] = 0;  // move null-terminator three positions back
  strcpy(filenameUBX, filename_NO_EXT);
  strcat(filenameUBX, ".ubx");
  strcpy(filenameSBP, filename_NO_EXT);
  strcat(filenameSBP, ".sbp");
  strcpy(filenameGPY, filename_NO_EXT);
  if(config.auto_upload_speedsurf){strcat(filenameGPY, "$.gpy");}//add $ to recognize .gpy file for auto-upload to speedsurf.app
  else {strcat(filenameGPY, ".gpy"); }  
  strcpy(filenameGPX, filename_NO_EXT);
  strcat(filenameGPX, ".gpx");
  if (config.logUBX == true) {
    if (sdOK) ubxfile = SD_MMC.open(filenameUBX, FILE_APPEND);
    if (LITTLEFS_OK) ubxfile = LITTLEFS.open(filenameUBX, FILE_APPEND);
    //ubxfile.setBufferSize(4096);
    //if(setvbuf(file, NULL, _IOFBF, 4096) != 0) {}//enlarge buffer SD handle error
  }
#if defined(GPY_H)
  if (config.logGPY == true) {
    if (sdOK) gpyfile = SD_MMC.open(filenameGPY, FILE_APPEND);
    if (LITTLEFS_OK) gpyfile = LITTLEFS.open(filenameGPY, FILE_APPEND);
    log_GPY_Header(gpyfile);
  }
#endif
  if (config.logSBP == true) {
    if (sdOK) sbpfile = SD_MMC.open(filenameSBP, FILE_APPEND);
    if (LITTLEFS_OK) sbpfile = LITTLEFS.open(filenameSBP, FILE_APPEND);
    log_header_SBP(sbpfile);
  }
  if (config.logGPX == true) {
    if (sdOK) gpxfile = SD_MMC.open(filenameGPX, FILE_APPEND);
    if (LITTLEFS_OK) gpxfile = LITTLEFS.open(filenameGPX, FILE_APPEND);
    log_GPX(GPX_HEADER, gpxfile);
  }
  if (config.logTXT == true) {
    if (sdOK) errorfile = SD_MMC.open(filenameERR, FILE_APPEND);
    if (LITTLEFS_OK) errorfile = LITTLEFS.open(filenameERR, FILE_APPEND);
  }
}
void Close_files(void) {
  log_GPX(GPX_END, gpxfile);
  gpxfile.close();
  ubxfile.close();
  errorfile.close();
  gpyfile.close();
  sbpfile.close();
}
void Flush_files(void) {
  if (config.sample_rate <= 10) {  //@18Hz still lost points !!!
    static int load_balance = 0;
    if (load_balance == 0) ubxfile.flush();
    if (load_balance == 1) errorfile.flush();
    if (load_balance == 2) gpyfile.flush();
    if (load_balance == 3) sbpfile.flush();
    if (load_balance == 4) {
      gpxfile.flush();
      load_balance = -1;
    }
    load_balance++;
  }
}
void Add_String(void) {
  strcat(dataStr, Buffer);  //add it onto the end
  strcat(dataStr, ";");     //append the delimeter
}
void Log_to_SD(void) {
  if (Time_Set_OK == true) {
  
    if (config.logUBX == true) {
      ubxfile.write(0xB5);
      ubxfile.write(0x62);
      ubxfile.write((const uint8_t *)&ubxMessage.navPvt, sizeof(ubxMessage.navPvt));

      static int old_nav_sat_message = 0;
      if (nav_sat_message != old_nav_sat_message) {
        old_nav_sat_message = nav_sat_message;
        ubxfile.write(0xB5);
        ubxfile.write(0x62);
        ubxfile.write((const uint8_t *)&ubxMessage.navSat, (ubxMessage.navSat.len + 6));  //nav_sat has a variable length, add chkA and chkB !!!
      }
    }
    if (config.logUBX_nav_sat) {  //only add navDOP msg to ubx file if nav_sat active
      ubxfile.write(0xB5);
      ubxfile.write(0x62);
      ubxfile.write((const uint8_t *)&ubxMessage.navDOP, sizeof(ubxMessage.navDOP));
    }
#if defined(GPY_H)
    if (config.logGPY == true) {
      log_GPY(gpyfile);
    }
#endif
    if (config.logSBP == true) {
      log_SBP(sbpfile);
    }
    if (config.logGPX == true) {
      log_GPX(GPX_FRAME, gpxfile);
    }
  }
}
// Loads the configuration from a file
void loadConfiguration(const char *filename, const char *filename_backup, Config &config) {
  // Open file for reading
  File file;
  if (sdOK){
    if (SD_MMC.exists(filename)) {
      Serial.println(F("open the config.txt"));
      file = SD_MMC.open(filename);
    } else if (SD_MMC.exists(filename_backup)) {
      Serial.println(F("open the config_backup.txt"));
      file = SD_MMC.open(filename_backup);
    } else {
      Serial.println(F("no configuration file found"));
      //wifi_search = 120;  //elongation SoftAP mode to 120s !!!
    }
  }
  if (LITTLEFS_OK){
    if (LITTLEFS.exists(filename)) {
      Serial.println(F("open the config.txt"));
      file = LITTLEFS.open(filename);
    } else if (LITTLEFS.exists(filename_backup)) {
      Serial.println(F("open the config_backup.txt"));
      file = LITTLEFS.open(filename_backup);
    } else {
      Serial.println(F("no configuration file found"));
      //wifi_search = 120;  //elongation SoftAP mode to 120s !!!
    }
  }
  StaticJsonDocument<2048> doc;
  // Deserialize the JSON document
  DeserializationError error = deserializeJson(doc, file);
  if (error) {
    Serial.println(F("Failed to deserialize file, using default configuration"));
    Serial.println(error.f_str());
    config.config_fail = 1;
  }
  // Copy values from the JsonDocument to the Config
  config.cal_bat = doc["cal_bat"] | 1.75;
  config.shutdown_voltage = doc["shutdown_voltage"] | 3.2;
  RTC_minimum_voltage_bat=config.shutdown_voltage;
  config.cal_speed = doc["cal_speed"] | 3.6;
  config.sample_rate = doc["sample_rate"] | 5;
  config.cpu_freq = doc["cpu_freq"] | 80;
  config.gnss = doc["gnss"] | 3;
  config.max_Svs = doc["max_Svs"] | 32;
  config.M10_min_elevation = doc["M10_min_elevation"] | 5;
  config.M10_full_power = doc["M10_full_power"] | 0;
  config.field = doc["speed_field"] | 1;
  config.speed_large_font = doc["speed_large_font"] | 0;
  config.bar_length = doc["bar_length"] | 1852;
  config.Stat_screens = doc["Stat_screens"] | 12;
  strlcpy(config.speed_screen,                      // <- destination
          doc["speed_screen"] | "1",          // <- source
          sizeof(config.speed_screen)); 
  strlcpy(config.stat_screen,                      // <- destination
          doc["stat_screen"] | "12",          // <- source
          sizeof(config.stat_screen)); 
  strlcpy(config.gpio12_screen,                      // <- destination
          doc["gpio12_screen"] | "4",          // <- source
          sizeof(config.gpio12_screen));         
  config.Stat_screens_time = doc["Stat_screens_time"] | 4;
  config.stat_speed = doc["stat_speed"] | 1;
  config.start_logging_speed = doc["start_logging_speed"] | 1;
  config.archive_days = doc["archive_days"] | 10;
  config.Board_Logo = doc["Board_Logo"] | 1;
  config.Sail_Logo = doc["Sail_Logo"] | 1;
  config.sleep_off_screen = doc["sleep_off_screen"] | 11;
  config.screen_orientation = doc["screen_orientation"]|0;
  config.logTXT = doc["logTXT"] | 1;
  config.logUBX = doc["logUBX"] | 0;
  if (config.sample_rate < 10) {
    config.logUBX_nav_sat = doc["logUBX_nav_sat"] | 0;
  } else {
    config.logUBX_nav_sat = 0;
  }
  config.logSBP = doc["logSBP"] | 0;
  config.logGPY = doc["logGPY"] | 1;
  config.auto_upload_speedsurf = doc["auto_upload_speedsurf"] | 0;
  config.logGPX = doc["logGPX"] | 0;
  config.file_date_time = doc["file_date_time"] | 1;
  config.dynamic_model = doc["dynamic_model"] | 0;  //sea model does not give a gps-fix if actual height is not on sea-level, better use model "portable"=0 !!!
  config.timezone = doc["timezone"] | 1.0;
  config.timezone_DST = doc["timezone_DST"]|1;
  if (doc["p1_lon"].is<const char*>()) {config.p1_lon = strtod(doc["p1_lon"], NULL);}
  if (doc["p1_lat"].is<const char*>()) {config.p1_lat = strtod(doc["p1_lat"], NULL);}
  if (doc["p2_lon"].is<const char*>()) {config.p2_lon = strtod(doc["p2_lon"], NULL);}
  if (doc["p2_lat"].is<const char*>()) {config.p2_lat = strtod(doc["p2_lat"], NULL);}
  strlcpy(config.UBXfile,                      // <- destination
          doc["UBXfile"] | "/ubxGPS",          // <- source
          sizeof(config.UBXfile));             // <- destination's capacity
  strlcpy(config.Sleep_info,                   // <- destination
          doc["Sleep_info"] | "My ID",         // <- source
          sizeof(config.Sleep_info));          // <- destination's capacity
  strcpy(RTC_Sleep_txt, config.Sleep_info);    //copy into RTC mem
  strlcpy(config.ssid,                         // <- destination
          doc["ssid"] | "ssid_not_set",             // <- source
          sizeof(config.ssid));                // <- destination's capacity
  strlcpy(config.password,                     // <- destination
          doc["password"] | "password",  // <- source
          sizeof(config.password));            // <- destination's capacity
  strlcpy(config.ssid2,                         // <- destination
          doc["ssid2"] | "ESP_GPS",             // <- source
          sizeof(config.ssid2));                // <- destination's capacity
  strlcpy(config.password2,                     // <- destination
          doc["password2"] | "password2",  // <- source
          sizeof(config.password2));            // <- destination's capacity        
                                               // Close the file (Curiously, File's destructor doesn't close the file)
  file.close();
  if (error) {
    Serial.println(config.cal_bat);
    Serial.println(config.cal_speed);
    Serial.println(config.sample_rate);
    Serial.println(config.logSBP);
    Serial.println(config.logUBX);
    Serial.println(config.ssid);
    Serial.println(config.password);
    Serial.println(config.Sail_Logo);
  }
  RTC_Board_Logo = config.Board_Logo;  //copy RTC memory !!
  RTC_Sail_Logo = config.Sail_Logo;    //copy to RTC memory !!
  RTC_calibration_bat = config.cal_bat;
  //config.cal_bat=RTC_calibration_bat; //stored in EEPROM !!!
  calibration_speed = config.cal_speed / 1000;  //3.6=km/h, 1.94384449 = knots, speed is now in mm/s
  //time_out_nav_pvt=(1000/config.sample_rate+75);//max time out = 175 ms
  RTC_SLEEP_screen = config.sleep_off_screen % 10;
  RTC_OFF_screen = config.sleep_off_screen / 10 % 10;
  if (config.file_date_time == 0) config.logTXT = 1;  //because txt file is needed for generating new file count !!
  config.screen_count= strlen(config.stat_screen)-1;
  config.speed_count =strlen(config.speed_screen)-1;
  config.gpio12_count =strlen(config.gpio12_screen)-1;
  config.field_actual=config.speed_screen[0];
  TimeZone_env(config.timezone);//to set the correct posic TZ string
  p1={config.p1_lon,config.p1_lat};
  p2={config.p2_lon,config.p2_lat};
  perpendicular_line(p1,p3,p1,500.0,&p2,&p4);
}
// Prints the content of a file to the Serial
void printFile(const char *filename) {
  // Open file for reading
  File file;
  if(sdOK) file = SD_MMC.open(filename);
  if(LITTLEFS_OK) file = LITTLEFS.open(filename);
  if (!file.available()) {
    Serial.println(F("Failed to read file"));
    return;
  }
  // Extract each characters by one by one
  while (file.available()) {
    Serial.print((char)file.read());
  }
  Serial.println();
  // Close the file
  file.close();
}
void AddString(void) {
  strcat(dataStr, Buffer);  //add it onto the end
  strcat(dataStr, ":");     //append the delimeter
}

void Model_info(int model) {
  if (config.logTXT) {
    char tekst[20] = "";
    char message[255] = "";
    errorfile.print("Dynamic model: ");
    if (model == 1) errorfile.print("Sea");
    else errorfile.print("Portable");
    strcat(message, " Msg_nr: ");
    dtostrf(nav_pvt_message, 1, 0, tekst);
    strcat(message, tekst);
    errorfile.println(message);
  }
}
void Session_info(GPS_data G) {
  char tekst[64] = "";
  char message[1024] = "";
  errorfile.print("T5 MAC adress: ");
  for (int i = 0; i < 6; i++) errorfile.print(mac[i], HEX);
  errorfile.println(" ");
  errorfile.println(SW_version);
  if(sdOK){
    sprintf(tekst,"SD_MMC Read speed= %d ms/MB Write speed= %d ms/MB s\n",SD_MMC_read_speed,SD_MMC_write_speed);
    strcat(message, tekst);
    }
  sprintf(tekst, "First fix : %d s\n", first_fix_GPS);
  strcat(message, tekst);
  sprintf(tekst, "Total time : %lu s\n", (millis() - start_logging_millis) / 1000);
  strcat(message, tekst);
  sprintf(tekst, "Total distance : %d m\n", (int)G.total_distance / 1000);
  strcat(message, tekst);
  sprintf(tekst, "Sample rate : %d Hz\n", config.sample_rate);
  strcat(message, tekst);
  sprintf(tekst, "CPU freq logging : %d MHz\n", config.cpu_freq);
  strcat(message, tekst);
  sprintf(tekst, "Speed calibration: %f \n", config.cal_speed);
  strcat(message, tekst);
  sprintf(tekst, "Lipo calibration: %.3f \n", RTC_calibration_bat);
  strcat(message, tekst);
  sprintf(tekst, "Timezone : %f h\n", config.timezone);
  strcat(message, tekst);
  sprintf(tekst, "tz offset (sec) : %ld \n", _timezone);
  strcat(message, tekst);
  strcat(message,TimeZone);
  strcat(message, "\nDynamic model: ");
  if (config.dynamic_model == 1) strcat(message, "Sea");
  else if (config.dynamic_model == 2) strcat(message, "Automotive");
  else strcat(message, "Portable");
  strcat(message, " \n");
  sprintf(tekst, "Max nr of sats for M10: %d \n", config.max_Svs);
  strcat(message, tekst);
  sprintf(tekst, "Ublox GNSS-enabled : %d\n", ubxMessage.monGNSS.enabled_Gnss);
  strcat(message, tekst);
  if (ubxMessage.monGNSS.enabled_Gnss == 3) strcat(message, "GNSS = GPS + GLONASS");                      //bitmask GAL BEI GLO GPS:0011 = 3
  if (ubxMessage.monGNSS.enabled_Gnss == 5) strcat(message, "GNSS = GPS + BEIDOU");                      //bitmask GAL BEI GLO GPS:0101 = 5
  if (ubxMessage.monGNSS.enabled_Gnss == 9) strcat(message, "GNSS = GPS + GALILEO");                     //bitmask GAL BEI GLO GPS:1001 = 9
  if (ubxMessage.monGNSS.enabled_Gnss == 13) strcat(message, "GNSS = GPS + GALILEO + BEIDOU");           //bitmask GAL BEI GLO GPS:1101 = 13
  if (ubxMessage.monGNSS.enabled_Gnss == 11) strcat(message, "GNSS = GPS + GLONASS + GALILEO");           //bitmask GAL BEI GLO GPS:1011 = 11
  if (ubxMessage.monGNSS.enabled_Gnss == 7) strcat(message, "GNSS = GPS + GLONASS + BEIDOU");             //bitmask GAL BEI GLO GPS:0111 = 7
  if (ubxMessage.monGNSS.enabled_Gnss == 15) strcat(message, "GNSS = GPS + GLONASS + GALILEO + BEIDOU");  //only M9 //bitmask GAL BEI GLO GPS:1111 = 15
  strcat(message, " \n");
  strcat(message, "Ublox SW-version : ");
  strcat(message, ubxMessage.monVER.swVersion);
  strcat(message, " \n");
  strcat(message, "Ublox HW-version : ");
  strcat(message, ubxMessage.monVER.hwVersion);
  strcat(message, " \n");
  sprintf(tekst,"Ublox minimal elevation Sats: %d \n",config.M10_min_elevation);
  strcat(message, tekst);
  if(config.M10_full_power) 
    sprintf(tekst,"M10 full power ON !\n");
  else
    sprintf(tekst,"M10 full power OFF !\n");
  strcat(message, tekst);
  if(config.M10_high_nav==3) 
    sprintf(tekst,"M10 high clockspeed !\n");
  else
    sprintf(tekst,"M10 default clockspeed !\n");
  strcat(message, tekst);
  if ((config.ublox_type == M10_9600BD) | (config.ublox_type == M10_38400BD)| (config.ublox_type == M10_115200BD)) 
    sprintf(tekst, "Ublox M10 ID = %02x%02x%02x%02x%02x%02x\n", ubxMessage.ubxId.ubx_id_1, ubxMessage.ubxId.ubx_id_2, ubxMessage.ubxId.ubx_id_3, ubxMessage.ubxId.ubx_id_4, ubxMessage.ubxId.ubx_id_5, ubxMessage.ubxId.ubx_id_6);
  if ((config.ublox_type == M8_9600BD) | (config.ublox_type == M8_38400BD))
    sprintf(tekst, "Ublox M8 ID = %02x%02x%02x%02x%02x\n", ubxMessage.ubxId.ubx_id_1, ubxMessage.ubxId.ubx_id_2, ubxMessage.ubxId.ubx_id_3, ubxMessage.ubxId.ubx_id_4, ubxMessage.ubxId.ubx_id_5);
  if ((config.ublox_type == M9_9600BD) | (config.ublox_type == M9_38400BD)|(config.ublox_type == M9_115200BD))
    sprintf(tekst, "Ublox M9 ID = %02x%02x%02x%02x%02x%02x\n", ubxMessage.ubxId.ubx_id_1, ubxMessage.ubxId.ubx_id_2, ubxMessage.ubxId.ubx_id_3, ubxMessage.ubxId.ubx_id_4, ubxMessage.ubxId.ubx_id_5, ubxMessage.ubxId.ubx_id_6);
  strcat(message, tekst);
  strcat(message, Ublox_type);
  strcat(message, " \n");
  errorfile.print(message);
}

void Session_results_M(GPS_speed M) {
  for (int i = 9; i > 4; i--) {
    char tekst[20] = "";
    char message[255] = "";
    int Calibration = config.cal_speed * 1000;
    dtostrf(M.avg_speed[i] * calibration_speed, 1, 3, tekst);
    strcat(message, tekst);
    if (Calibration == 3600) strcat(message, " km/h ");
    if ((Calibration >= 1943) & (Calibration <= 1945)) strcat(message, " knots ");
    dtostrf(M.time_hour[i], 1, 0, tekst);
    strcat(message, tekst);
    strcat(message, ":");
    dtostrf(M.time_min[i], 1, 0, tekst);
    strcat(message, tekst);
    strcat(message, ":");
    dtostrf(M.time_sec[i], 1, 0, tekst);
    strcat(message, tekst);
    strcat(message, " Distance: ");
    dtostrf(M.m_Distance[i] / 1000.0f / config.sample_rate, 1, 2, tekst);
    strcat(message, tekst);
    strcat(message, " Msg_nr: ");
    dtostrf(M.message_nr[i], 1, 0, tekst);
    strcat(message, tekst);
    strcat(message, " Samples: ");
    dtostrf(M.nr_samples[i], 1, 0, tekst);
    strcat(message, tekst);
    strcat(message, " Run: ");
    dtostrf(M.this_run[i], 1, 0, tekst);
    strcat(message, tekst);
    strcat(message, " M");
    dtostrf(M.m_set_distance, 1, 0, tekst);
    strcat(message, tekst);
    strcat(message, "\n");
    errorfile.print(message);
  }
}
void Session_results_S(GPS_time S) {
  char tekst[20] = "";
  char message[255] = "";
  int Calibration = config.cal_speed * 1000;
  dtostrf(S.avg_5runs * calibration_speed, 1, 3, tekst);
  strcat(message, tekst);
  if (Calibration == 3600) strcat(message, " km/h avg 5_best_runs\n");
  else if ((Calibration >= 1943) & (Calibration <= 1945)) strcat(message, " knots avg 5_best_runs\n");
  else strcat(message, " avg 5_best_runs\n");
  //errorfile.open();
  errorfile.print(message);
  //errorfile.close();
  //appendFile(SD,filenameERR,message);
  for (int i = 9; i > 4; i--) {
    char tekst[45] = "";
    char message[255] = "";
    dtostrf(S.avg_speed[i] * calibration_speed, 1, 3, tekst);
    strcat(message, tekst);
    if (Calibration == 3600) strcat(message, " km/h ");
    if ((Calibration >= 1943) & (Calibration <= 1945)) strcat(message, " knots ");
    dtostrf(S.time_hour[i], 1, 0, tekst);
    strcat(message, tekst);
    strcat(message, ":");
    dtostrf(S.time_min[i], 1, 0, tekst);
    strcat(message, tekst);
    strcat(message, ":");
    dtostrf(S.time_sec[i], 1, 0, tekst);
    strcat(message, tekst);
    strcat(message, " Run: ");
    dtostrf(S.this_run[i], 1, 0, tekst);
    strcat(message, tekst);
    strcat(message, " S");
    dtostrf(S.time_window, 1, 0, tekst);
    strcat(message, tekst);
    if (config.logUBX_nav_sat) {
      sprintf(tekst, " CNO Max: %u Avg: %u Min: %u nr Sat: %u\n", S.Max_cno[i], S.Mean_cno[i], S.Min_cno[i], S.Mean_numSat[i]);
      strcat(message, tekst);
    } else strcat(message, "\n");
    errorfile.print(message);
  }
}
void Session_results_Alfa(Alfa_speed A, GPS_speed M) {
  for (int i = 9; i > 4; i--) {
    char tekst[20] = "";
    char message[255] = "";
    int Calibration = config.cal_speed * 1000;
    dtostrf(A.avg_speed[i] * calibration_speed, 1, 3, tekst);
    strcat(message, tekst);
    if (Calibration == 3600) strcat(message, " km/h ");
    if (Calibration == 1943) strcat(message, " knots ");
    dtostrf(sqrt((float)A.real_distance[i]), 1, 2, tekst);
    strcat(message, tekst);
    strcat(message, " m ");
    dtostrf(A.alfa_distance[i], 1, 1, tekst);
    strcat(message, tekst);
    strcat(message, " m ");
    dtostrf(A.time_hour[i], 1, 0, tekst);
    strcat(message, tekst);
    strcat(message, ":");
    dtostrf(A.time_min[i], 1, 0, tekst);
    strcat(message, tekst);
    strcat(message, ":");
    dtostrf(A.time_sec[i], 1, 0, tekst);
    strcat(message, tekst);
    strcat(message, " Run: ");
    dtostrf(A.this_run[i], 1, 0, tekst);
    strcat(message, tekst);
    strcat(message, " Msg_nr: ");
    dtostrf(A.message_nr[i], 1, 0, tekst);
    strcat(message, tekst);
    strcat(message, " Alfa");
    dtostrf(M.m_set_distance, 1, 0, tekst);
    strcat(message, tekst);
    strcat(message, "\n");
    errorfile.print(message);
  }
}
void Session_results_track(void){
   // char tekst[64] = "";
    char message[255] = "";
    sprintf(message,"Track Length %.2f , Start %.7f lat %.7f lon, Finish %.7f lat %.7f lon \n",trajectAfstandMeters,config.p1_lat,config.p1_lon,config.p2_lat,config.p2_lon);
    errorfile.print(message);
    //terug leeg schrijven
    message[0] = '\0'; 
    for (int i = 0; i < 10; i++) {
      message[0] = '\0'; 
      sprintf(message,"%d Track %.7f Doppler %.7f Proj_doppler %.7f Time %d:%d \n",i+1,track_speed[9-i] * calibration_speed,doppler_speed[9-i] * calibration_speed,projected_doppler_speed[9-i] * calibration_speed,track_hour[9-i],track_minute[9-i]);
      errorfile.print(message);
      }

}
void Session_gpstc(char* gpstc){
  errorfile.print(gpstc);
}
void TimeZone_env (float timezone){     //without daylight saving, standard TZ strirng
  int hours=(int)(timezone);
  int minutes=abs((int)(timezone*60)%60);
  char time_noDST[64]="GMT0";
  if(hours>0){
    sprintf(time_noDST,"CET-%d:%02d",hours,minutes); //default TZ string is CET + timezone offset, no DST possible
    }
  else{
    sprintf(time_noDST,"CET+%d:%02d",-hours,minutes);
    }  
  strcpy(TimeZone,time_noDST); //standard timezone without daylightsaving
  if(config.timezone_DST){
    switch((int)(timezone*100)){
      case 0: strcpy (TimeZone,"GMT0BST,M3.5.0/1,M10.5.0");break;//Europe/ London
      case 100: strcpy (TimeZone,"CET-1CEST,M3.5.0,M10.5.0/3");break;//Europe / Brussels
      case 200: strcpy (TimeZone,"EET-2EEST,M3.5.0,M10.5.0/3");break;
      case 300: strcpy (TimeZone,"<-03>3<-02>,M3.2.0,M11.1.0");break;
      case 500: strcpy (TimeZone,"CST5CDT,M3.2.0/0,M11.1.0/1");break;//America/Detroit
      case 600: strcpy (TimeZone,"CST6CDT,M3.2.0,M11.1.0");break;//America/Chicago
      case 700: strcpy (TimeZone,"MST7MDT,M3.2.0,M11.1.0");break;//America/Boise
      case 800: strcpy (TimeZone,"PST8PDT,M3.2.0,M11.1.0");break;//America/Los_Angeles
      case 950: strcpy (TimeZone,"ACST-9:30ACDT,M10.1.0,M4.1.0/3");break;//Australia/Adelaide
      case 1000: strcpy (TimeZone,"AEST-10AEDT,M10.1.0,M4.1.0/3");break;//Antarctica/Macquarie
      case 1050: strcpy (TimeZone,"<+1030>-10:30<+11>-11,M10.1.0,M4.1.0");break;//Australia/Lord_Howe
      case 1200: strcpy (TimeZone,"NZST-12NZDT,M9.5.0,M4.1.0/3");break;//Antarctica/McMurdo
      case -100: strcpy (TimeZone,"<-01>1<+00>,M3.5.0/0,M10.5.0/1");break;
      case -200: strcpy (TimeZone,"IST-2IDT,M3.4.4/26,M10.5.0");break;

    } 
  }
}
uint64_t Free_space(void){
  uint64_t free_kbytes=0;
  if(LITTLEFS_OK) free_kbytes = (LITTLEFS.totalBytes() - LITTLEFS.usedBytes())/1024;
  if(sdOK) {
    uint64_t totalBytes=SD_MMC.totalBytes();
    uint64_t usedBytes=SD_MMC.usedBytes();
    free_kbytes=(totalBytes-usedBytes)/1024;
    }
  return free_kbytes;
}
int Logtime_left (uint64_t kbytes){
  uint64_t free_kbytes=0;
    if(LITTLEFS_OK) free_kbytes = (LITTLEFS.totalBytes() - LITTLEFS.usedBytes())/1024;
    if(sdOK) {
        uint64_t totalBytes=SD_MMC.totalBytes();
        uint64_t usedBytes=SD_MMC.usedBytes();
        free_kbytes=(totalBytes-usedBytes)/1024;
        }
    int data_rate = (config.logGPY*24+config.logUBX*100+config.logSBP*32+1)*config.sample_rate+config.logGPX*230;//+1 to prevent divide by 0 !!!
    uint64_t logtime_left_sec = free_kbytes/data_rate*1024;
    int logtime_left_min = logtime_left_sec/60; 
    return logtime_left_min;   
}
void testFileIO(fs::FS &fs, const char * path){
  File file = fs.open(path);
  static uint8_t buf[512];
  size_t len = 0;
  uint32_t start = millis();
  uint32_t end = start;
  if(file){
    len = file.size();
    size_t flen = len;
    start = millis();
    while(len){
      size_t toRead = len;
      if(toRead > 512){
        toRead = 512;
      }
      file.read(buf, toRead);
      len -= toRead;
    }
    end = millis() - start;
    SD_MMC_read_speed=end;
    Serial.printf("%u bytes read for %u ms\n", flen, end);
    file.close();
  } else {
    Serial.println("Failed to open file for reading");
  }
  file = fs.open(path, FILE_WRITE);
  if(!file){
    Serial.println("Failed to open file for writing");
    return;
  }

  size_t i;
  start = millis();
  for(i=0; i<2048; i++){
    file.write(buf, 512);
  }
  end = millis() - start;
  SD_MMC_write_speed=end;
  Serial.printf("%u bytes written for %u ms\n", 2048 * 512, end);
  file.close();
}
