RP6conrad/ESP-GPS-Logger/Ublox.h

#ifndef UBLOX_H
#define UBLOX_H
//https://github.com/iforce2d/inavFollowme/blob/master/FollowMeTag/GPS.h
//https://content.u-blox.com/sites/default/files/MAX-M10S_IntegrationManual_UBX-20053088.pdf  M10 high performance mode
#include "Arduino.h"
#include "sys/time.h"
#include "SD_card.h"
#include <driver/rtc_io.h>
#include <driver/gpio.h>

#define RXD2 32  //geel is Tx Ublox, Beitian wit is Tx
#define TXD2 33  //groen is Rx Ublox, Beitian groen is Rx
//ublox M8, baudrate setting and only ubx out is one command !!!!
const char UBLOX_UBX_BD9600[] PROGMEM = {
  0xB5, 0x62, 0x06, 0x00, 0x14, 0x00, 0x01, 0x00, 0x00, 0x00, 0xD0, 0x08, 0x00, 0x00, 0x80, 0x25, 0x00, 0x00, 0x23, 0x00, 0x01, 0x00, 0x00, 0x00, 0x00, 0x00, 0xBC, 0x89
}; 
const char UBLOX_UBX_BD19200[] PROGMEM = {
  0xB5, 0x62, 0x06, 0x00, 0x14, 0x00, 0x01, 0x00, 0x00, 0x00, 0xD0, 0x08, 0x00, 0x00, 0x00, 0x4B, 0x00, 0x00, 0x23, 0x00, 0x01, 0x00, 0x00, 0x00, 0x00, 0x00, 0x62, 0x2B
};  //set baudrate to 19200, only UBX out
const char UBLOX_UBX_BD38400[] PROGMEM = {
  0xB5, 0x62, 0x06, 0x00, 0x14, 0x00, 0x01, 0x00, 0x00, 0x00, 0xD0, 0x08, 0x00, 0x00, 0x00, 0x96, 0x00, 0x00, 0x23, 0x00, 0x01, 0x00, 0x00, 0x00, 0x00, 0x00, 0xAD, 0x64
};                                                                                                                                             //28 bytes
const char UBLOX_UBX_NAVPVT_ON[] PROGMEM = { 0xB5, 0x62, 0x06, 0x01, 0x08, 0x00, 0x01, 0x07, 0x00, 0x01, 0x00, 0x00, 0x00, 0x00, 0x18, 0xE1 };  //NAV-PVT on 16 bytes
const char UBLOX_UBX_NAVDOP_ON[] PROGMEM = {0xB5,0x62,0x06,0x01,0x08,0x00,0x01,0x04,0x00,0x01,0x00,0x00,0x00,0x00,0x15,0xCC,};  //NAV-DOP on
const char UBLOX_UBX_NAVSAT_ON[] PROGMEM = {0xB5,0x62,0x06,0x01,0x08,0x00,0x01,0x35,0x00,0x0A,0x00,0x00,0x00,0x00,0x4F,0x50};//NAV-SAT on, but 10% rate of NAV PVT !!

const char UBLOX_M10_BEIDOU_OFF[] PROGMEM = {
0xB5,0x62,0x06,0x8A,0x09,0x00,0x01,0x01,0x00,0x00,0x22,0x00,0x31,0x10,0x00,0xFE,0x97
};
const char UBLOX_M10_BEIDOU_B1_OFF[] PROGMEM = {
0XB5,0X62,0X06,0X8A,0X09,0X00,0X01,0X01,0X00,0X00,0X0D,0X00,0X31,0X10,0X00,0XE9,0X2E
};
const char UBLOX_M10_BEIDOU_B1C_ON[] PROGMEM = {
0XB5,0X62,0X06,0X8A,0X09,0X00,0X01,0X01,0X00,0X00,0X0F,0X00,0X31,0X10,0X01,0XEC,0X39
};
const char UBLOX_M10_GAL_ON[] PROGMEM = {
0xB5,0x62,0x06,0x8A,0x09,0x00,0x01,0x01,0x00,0x00,0x21,0x00,0x31,0x10,0x01,0xFE,0x93
};
const char UBLOX_M10_GAL_OFF[] PROGMEM = {
0XB5,0X62,0X06,0X8A,0X09,0X00,0X01,0X01,0X00,0X00,0X21,0X00,0X31,0X10,0X00,0XFD,0X92
};
const char UBLOX_M10_GLONASS_ON[] PROGMEM = {//GLONASS  enable
0XB5,0X62,0X06,0X8A,0X09,0X00,0X01,0X01,0X00,0X00,0X25,0X00,0X31,0X10,0X01,0X02,0XA7
};
const char UBLOX_M10_GLONASS_OFF[] PROGMEM = {//GLONASS disable
0XB5,0X62,0X06,0X8A,0X09,0X00,0X01,0X01,0X00,0X00,0X25,0X00,0X31,0X10,0X00,0X01,0XA6
};
const char UBLOX_M10_4GNSS[] PROGMEM = {//GPS+GAL+BEIDOU_B1C+GLONASS
0XB5,0X62,0X06,0X8A,0X13,0X00,0X01,0X01,0X00,0X00,0X0D,0X00,0X31,0X10,0X00,0X0F,0X00,0X31,0X10,0X01,0X25,0X00,0X31,0X10,0X01,0XAB,0X1B
};
const char UBLOX_M10_NMEA_OFF[] PROGMEM = {  //NMEA OFF, generated with ucenter2 !!
0xB5,0x62,0x06,0x8A,0x09,0x00,0x01,0x01,0x00,0x00,0x02,0x00,0x74,0x10,0x00,0x21,0xC0
};
const char UBLOX_M10_UBX[] PROGMEM = {  //CFG-UART1OUTPROT-UBX = 1, generated with ucenter2 !!
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
0x05,0xDE,0xAE
};
const char UBX_M10_FULL_POWER_MODE[] PROGMEM = {
0xB5, 0x62, 0x06, 0x8A, 0x09, 0x00, 0x00, 0x01, 0x00, 0x00, 0x11, 0x00, 0xA3, 0x20, 0x00, 0xDE, 0xDB
};

const char UBX_MON_GNSS[] PROGMEM = {0xB5,0x62,0x0A,0x28,0x00,0x00,0x32,0xA0};//poll GNSS setting
const char UBX_MON_VER[] PROGMEM =  {0xB5,0x62,0x0A,0x04,0x00,0x00,0x0E,0x34};//poll SW version
const char UBX_NAV_SAT[] PROGMEM =  {0xB5,0x62,0x01,0x35,0x00,0x00,0x36,0xA3};//poll NAV_SAT
const char UBX_ID[] PROGMEM = {0xB5, 0x62, 0x27, 0x03, 0x00, 0x00, 0x2A, 0xA5}; //poll unique ID B5 62 27 03 00 00 2A A5 


const unsigned char UBX_HEADER[] = { 0xB5, 0x62 };
const unsigned char NAV_DUMMY_HEADER[] = { 0x01, 0x00 };
const unsigned char NAV_PVT_HEADER[] = { 0x01, 0x07 };
const unsigned char NAV_ACK_HEADER[] = { 0x05, 0x01 };
const unsigned char NAV_NACK_HEADER[] = { 0x05, 0x00 };
const unsigned char NAV_ID_HEADER[] = { 0x27, 0x03 };
const unsigned char MON_GNSS_HEADER[] = { 0x0A, 0x28 };
const unsigned char NAV_DOP_HEADER[] = { 0x01, 0x04 };
const unsigned char MON_VER_HEADER[] = { 0x0A, 0x04 };
const unsigned char NAV_SAT_HEADER[] = { 0x01, 0x35 };
enum _ubxMsgType {
  MT_NONE,
  MT_NAV_DUMMY,
  MT_NAV_PVT,
  MT_NAV_ACK,
  MT_NAV_NACK,
  MT_NAV_ID,
  MT_MON_GNSS,
  MT_NAV_DOP,
  MT_MON_VER,
  MT_NAV_SAT
};
struct NAV_DUMMY {
  unsigned char cls;
  unsigned char id;
  unsigned short len;
  unsigned char msg_cls;
  unsigned char msg_id;
  unsigned char chkA;
  unsigned char chkB;
}__attribute__((__packed__));
struct NAV_PVT {  // 88 bytes payload, 92 bytes total, with Beitian BN220 100 bytes total ????(0xB5,0x62,....,chkA,chkB
  unsigned char cls;
  unsigned char id;
  unsigned short len;
  unsigned long iTOW;        // GPS time of week of the navigation epoch (ms)
  unsigned short year;       // Year (UTC)
  unsigned char month;       // Month, range 1..12 (UTC)
  unsigned char day;         // Day of month, range 1..31 (UTC)
  unsigned char hour;        // Hour of day, range 0..23 (UTC)
  unsigned char minute;      // Minute of hour, range 0..59 (UTC)
  unsigned char second;      // Seconds of minute, range 0..60 (UTC)
  char valid;                // Validity Flags (see graphic below)
  unsigned long tAcc;        // Time accuracy estimate (UTC) (ns)
  long nano;                 // Fraction of second, range -1e9 .. 1e9 (UTC) (ns)
  unsigned char fixType;     // GNSSfix Type, range 0..5
  char flags;                // Fix Status Flags
  unsigned char reserved1;   // reserved
  unsigned char numSV;       // Number of satellites used in Nav Solution
  long lon;                  // Longitude (deg)
  long lat;                  // Latitude (deg)
  long height;               // Height above Ellipsoid (mm)
  long hMSL;                 // Height above mean sea level (mm)
  unsigned long hAcc;        // Horizontal Accuracy Estimate (mm)
  unsigned long vAcc;        // Vertical Accuracy Estimate (mm)
  long velN;                 // NED north velocity (mm/s)
  long velE;                 // NED east velocity (mm/s)
  long velD;                 // NED down velocity (mm/s)
  long gSpeed;               // Ground Speed (2-D) (mm/s)
  long heading;              // Heading of motion 2-D (deg)
  unsigned long sAcc;        // Speed Accuracy Estimate
  unsigned long headingAcc;  // Heading Accuracy Estimate
  unsigned short pDOP;       // Position dilution of precision
  short reserved2;           // Reserved
  unsigned long reserved3;   // Reserved
  long headVeh;              //only valid for adr4.1, beitian bn220 !
  short magDec;              //only valid for adr4.1,beitian bn220 !
  short magAcc;              //only valid for adr4.1,beitian bn220 !
  unsigned char chkA;
  unsigned char chkB;
}__attribute__((__packed__));
struct NAV_ACK {
  unsigned char cls;
  unsigned char id;
  unsigned short len;
  unsigned char msg_cls;
  unsigned char msg_id;
  unsigned char chkA;
  unsigned char chkB;
}__attribute__((__packed__));
struct NAV_NACK {
  unsigned char cls;
  unsigned char id;
  unsigned short len;
  unsigned char msg_cls;
  unsigned char msg_id;
  unsigned char chkA;
  unsigned char chkB;
}__attribute__((__packed__));
struct NAV_ID {
  unsigned char cls;
  unsigned char id;
  unsigned short len;
  byte Version;
  byte reserved1;
  byte reserved2;
  byte reserved3;
  byte ubx_id_1;
  byte ubx_id_2;
  byte ubx_id_3;
  byte ubx_id_4;
  byte ubx_id_5;//M8 has only 5 byte ID !
  byte ubx_id_6;//M10 appeared to have 6 byte ID !!!
  unsigned char chkA;
  unsigned char chkB;
}__attribute__((__packed__));

struct MON_GNSS {
  unsigned char cls;
  unsigned char id;
  unsigned short len;
  byte Version;
  byte supported_Gnss;
  byte default_Gnss;
  byte enabled_Gnss;
  byte simultaneous;
  byte reserved1;
  byte reserved2;
  byte reserved3;
  unsigned char chkA;
  unsigned char chkB;
}__attribute__((__packed__));
struct NAV_DOP {  //payload 18 bytes, total 22 bytes, without (__packed__) 24 bytes !!!
  unsigned char cls;
  unsigned char id;
  unsigned short len;
  unsigned long iTOW;//4
  unsigned short gDOP;//6
  unsigned short pDOP;//8
  unsigned short tDOP;//10
  unsigned short vDOP;//12
  unsigned short hDOP;//14
  unsigned short nDOP;//16
  unsigned short eDOP;//18
  unsigned char chkA;
  unsigned char chkB;
}__attribute__((__packed__));
struct VER_EXT{
  char extension[30];
}__attribute__((__packed__));
struct MON_VER {
        unsigned char cls;
        unsigned char id;
        unsigned short len;
        char swVersion[30];
        char hwVersion[10];
        VER_EXT ext[6];         
        unsigned char chkA;
        unsigned char chkB;
    }__attribute__((__packed__));
struct sVs_NAV_SAT{
        byte gnssId;
        byte svId;
        byte cno;
        int8_t elev;
        short azim;
        short prRes;
        unsigned long X4;//bit3 = 1  : sV is used in navigation solution
}__attribute__((__packed__));   
struct NAV_SAT{
        unsigned char cls;
        unsigned char id;
        unsigned short len;//8 + 12*numSV !
        unsigned long iTOW;//4
        byte version;
        byte numSvs;
        byte reserved1;
        byte reserved2;
        sVs_NAV_SAT sat[92];//for M10, how many channels ???
        unsigned char chkA;//checksum moves with payload, only with 92 sats correct !!!
        unsigned char chkB;
}__attribute__((__packed__));
struct UBXMessage {//was union, but messages are overwritten by next message
  NAV_DUMMY navDummy;
  NAV_PVT navPvt;
  NAV_DOP navDOP;
  NAV_ACK navAck;
  NAV_NACK navNack;
  NAV_ID ubxId; 
  MON_GNSS monGNSS;
  MON_VER monVER;
  NAV_SAT navSat;
}__attribute__((__packed__));

extern UBXMessage ubxMessage;  //declaration here, definition in Ublox.cpp
extern bool sdOK;
//extern int config.ublox_type;
extern char dataStr[255];  //string for logging NMEA in txt, test for write 2000 chars !!
extern char Buffer[50];
void calcChecksum(unsigned char* CK,int msgType,int msgSize);
boolean compareMsgHeader(const unsigned char* msgHeader);
void Ublox_on();
void Ublox_off();
void Ublox_serial2(int delay_ms);
void Init_ublox(void);
void Set_rate_ublox(int);
void Init_ubloxM10(void);
void Set_rate_ubloxM10(int rate);
int Set_GPS_Time(float time_offset);
int processGPS();
int Auto_detect_ublox();
int Check_M10_nav_rate(void);
int Set_M10_high_nav_rate(void);
void sendNavSpgInfilMaxSvs(uint8_t maxSvs);
void build_ubx_cfg_min_elevation(int8_t angle_deg);
#endif
